beegee-tokyo/RAK4631-RAK12014-Waterlevel/rename.py

import datetime

Import("env")

my_flags = env.ParseFlags(env['BUILD_FLAGS'])
defines = {k: v for (k, v) in my_flags.get("CPPDEFINES")}

build_tag = "RAK_"

version_tag_1 = defines.get("SW_VERSION_1")
version_tag_2 = defines.get("SW_VERSION_2")
version_tag_3 = defines.get("SW_VERSION_3")
build_date = datetime.datetime.now().strftime('%Y-%m-%d-%H-%M-%S')

env.Replace(PROGNAME="../../../Generated/WisBlock_WL_V%s.%s.%s_%s" % (version_tag_1,version_tag_2,version_tag_3,build_date))
